Injenus/Inj_Bot_3.0/layout_images/type1.png

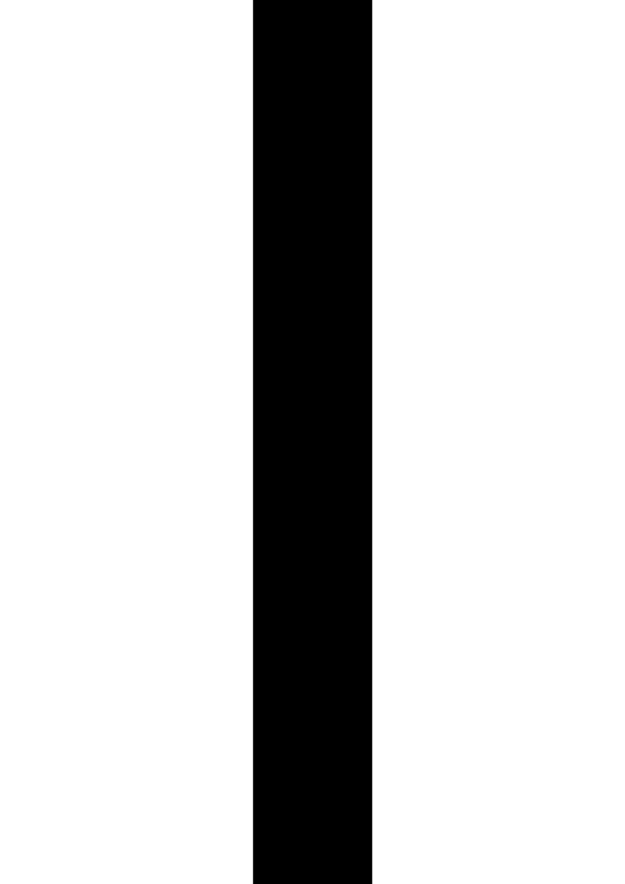
layout_images/type1.png
