Injenus/Inj_Bot_3.0/layout_images/type2.png

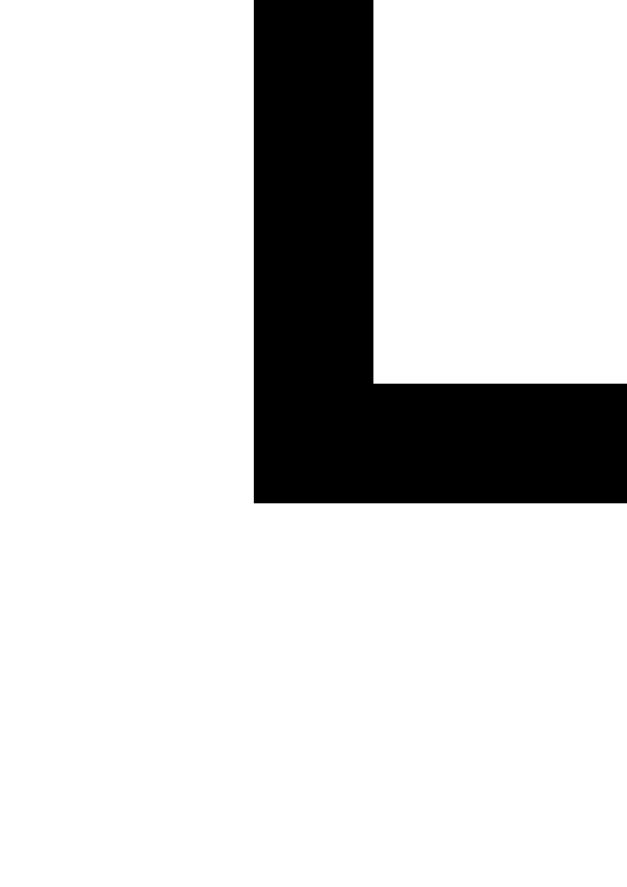
layout_images/type2.png
