Injenus/Inj_Bot_3.0/manipulator_view/workspace_points_1.png

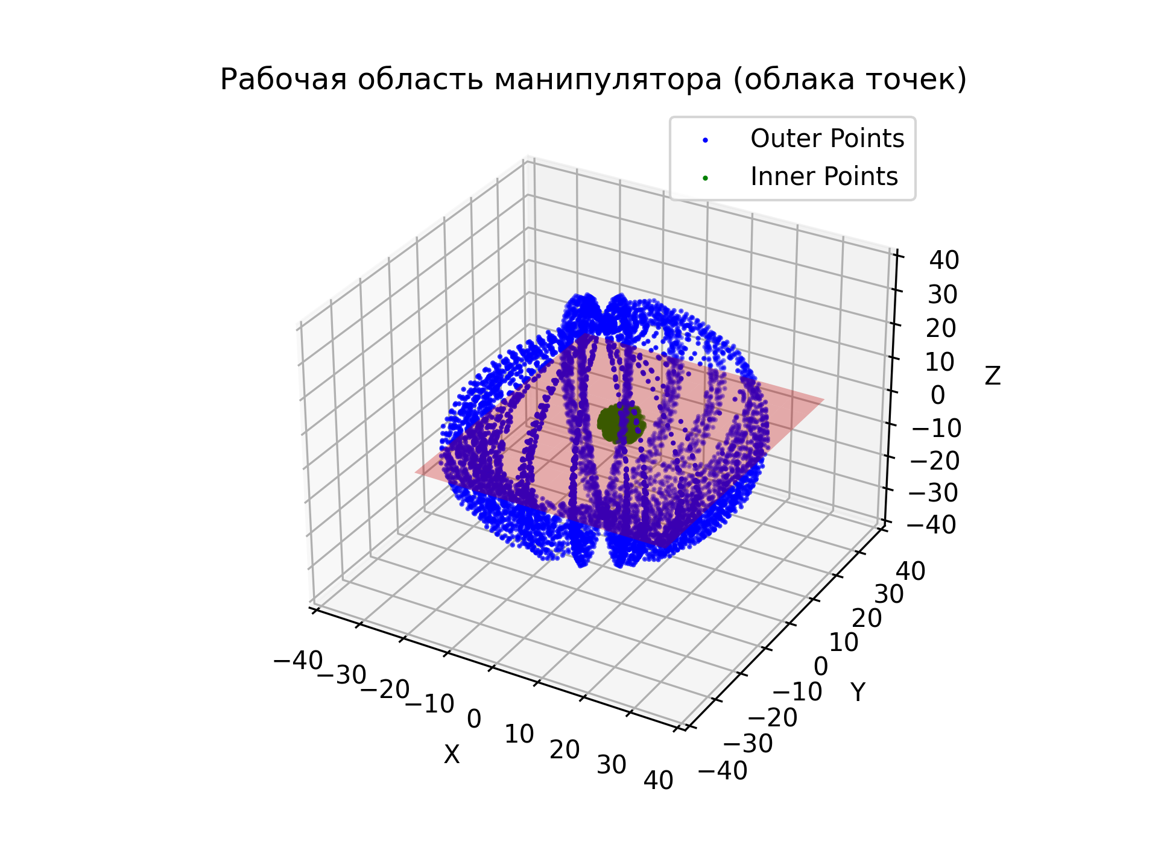
manipulator_view/workspace_points_1.png
