Injenus/Inj_Bot_3.0/manipulator_view/workspace_polygs_1.png

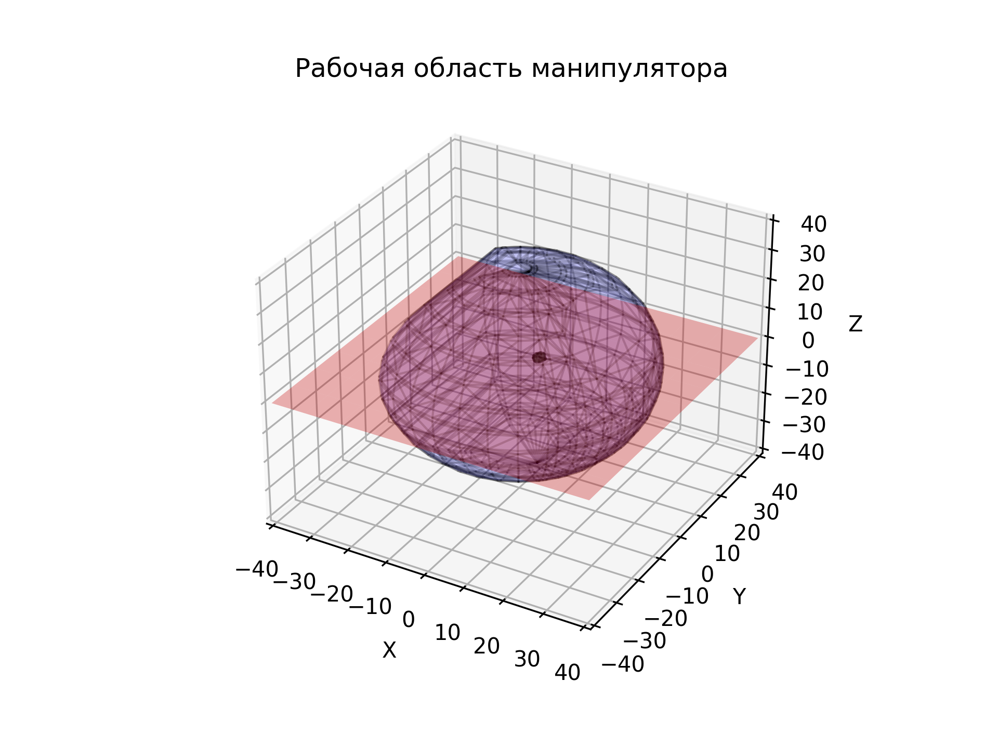
manipulator_view/workspace_polygs_1.png
