Injenus/Inj_Bot_3.0/neural_learn/runs/detect/fruit_detector/confusion_matrix.png

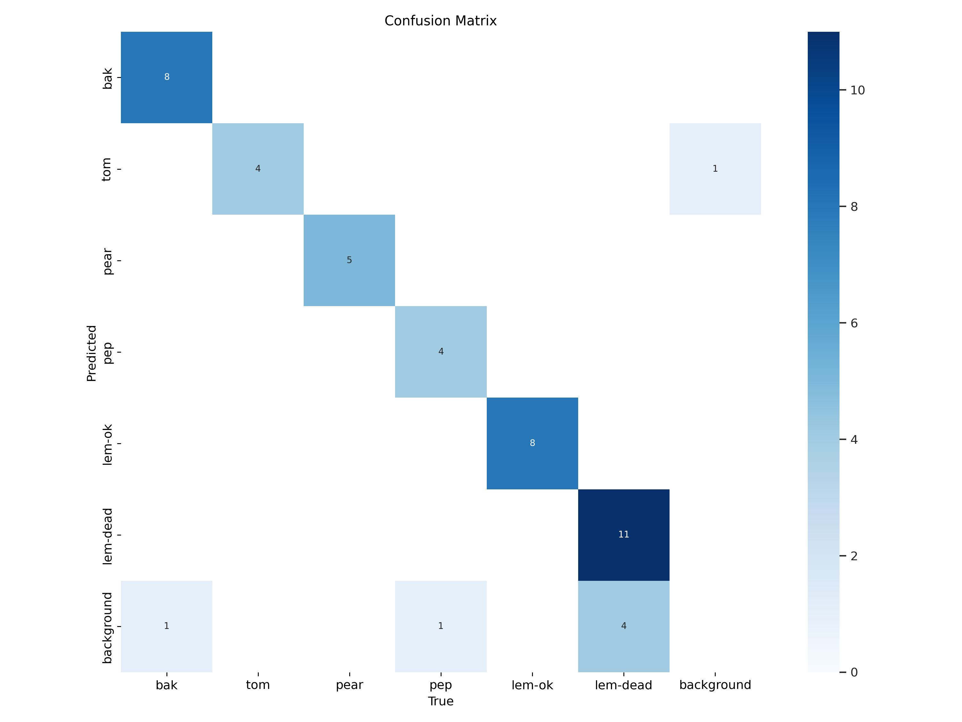
neural_learn/runs/detect/fruit_detector/confusion_matrix.png
