Injenus/Inj_Bot_3.0/neural_learn/runs/detect/fruit_detector/confusion_matrix_normalized.png

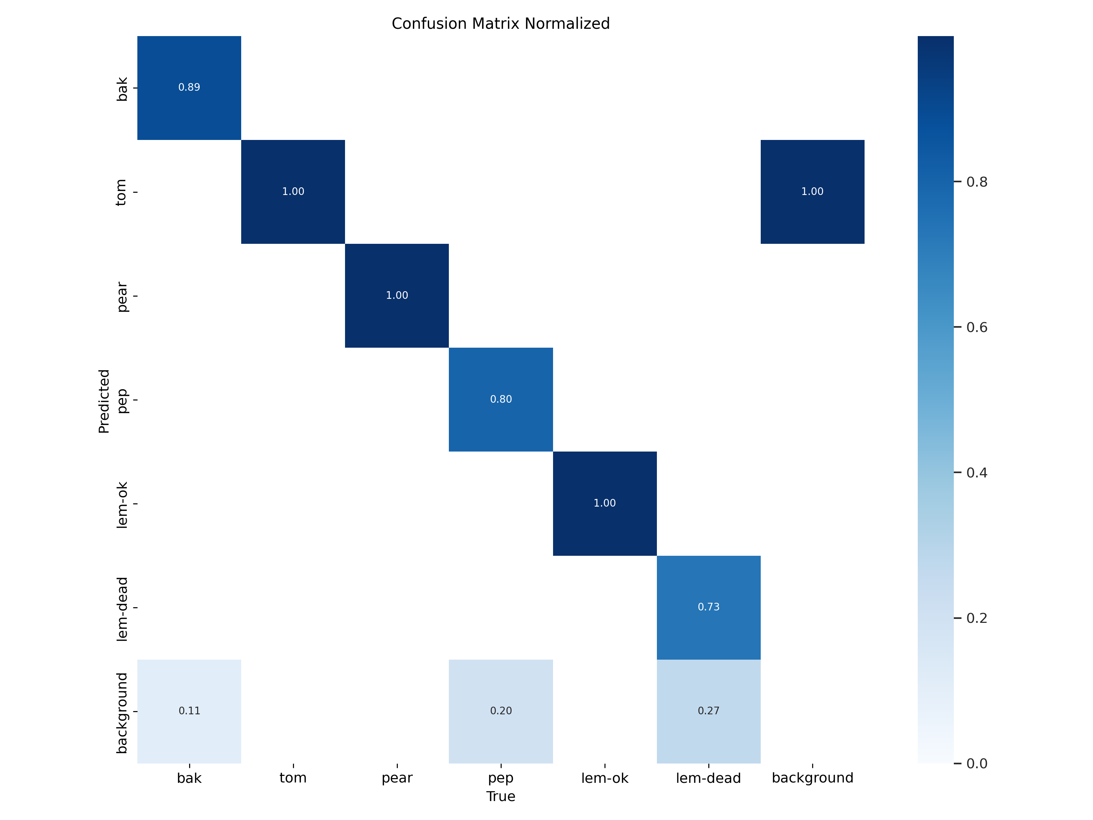
neural_learn/runs/detect/fruit_detector/confusion_matrix_normalized.png
