Injenus/Inj_Bot_3.0/neural_learn/runs/detect/fruit_detector/F1_curve.png

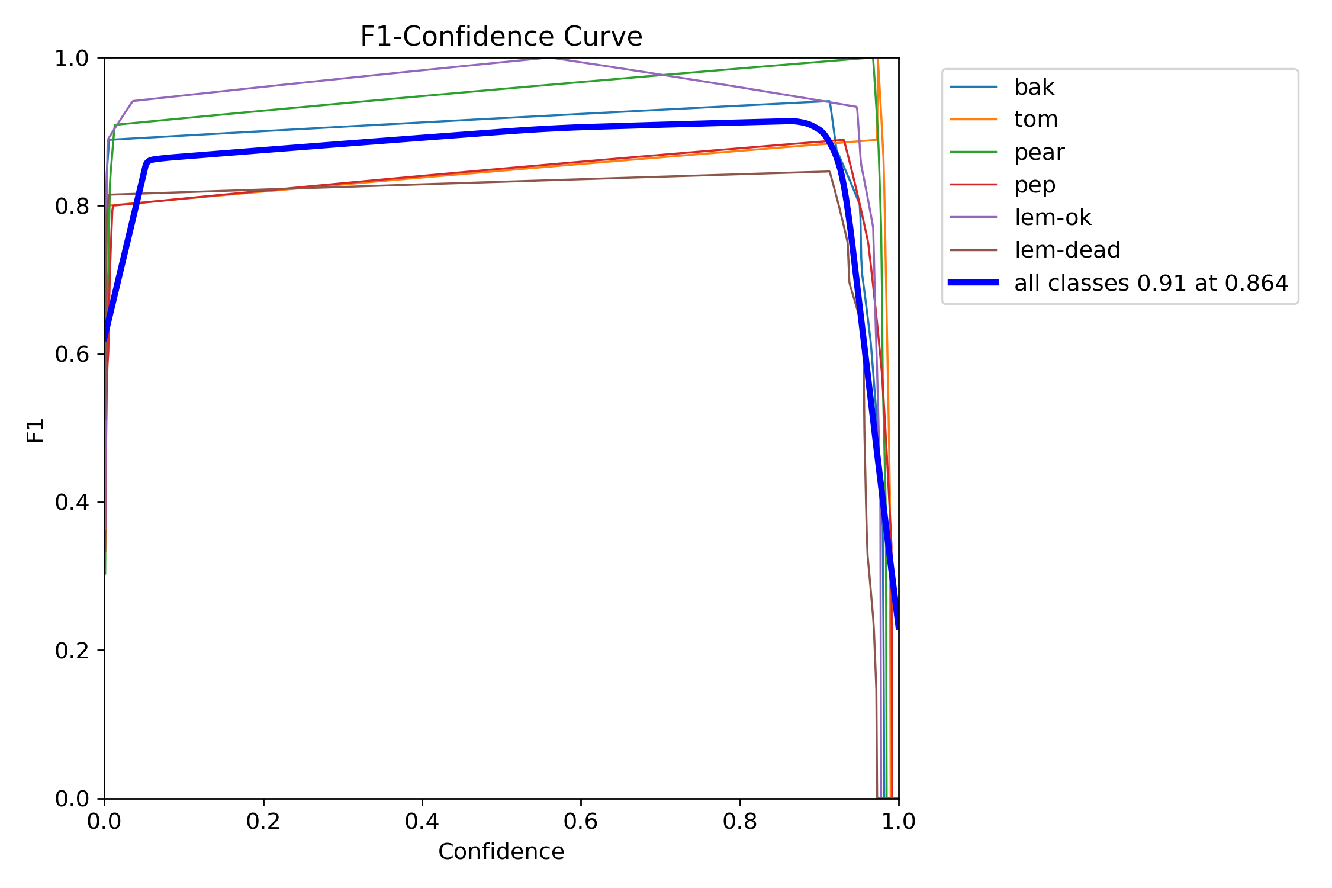
neural_learn/runs/detect/fruit_detector/F1_curve.png
