Injenus/Inj_Bot_3.0/bot_parts/body.stl

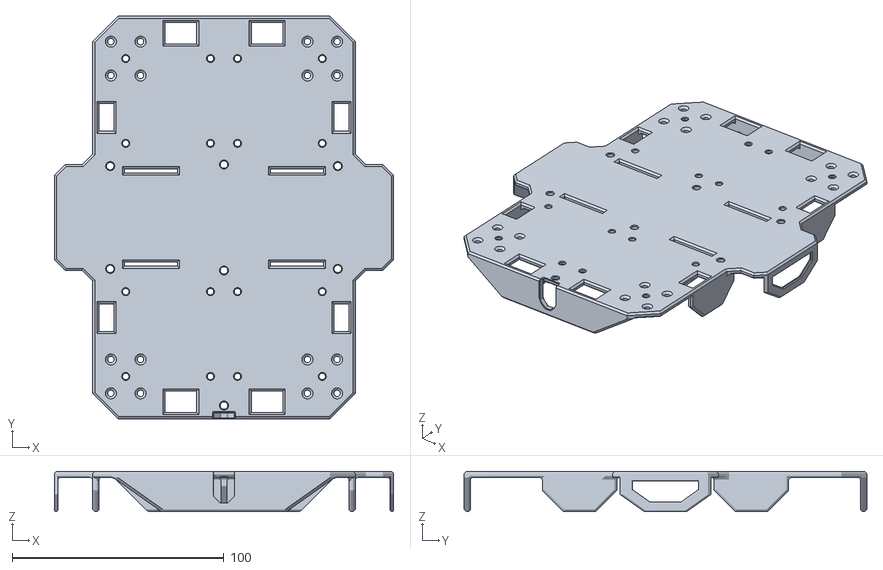
[picture p28: CAD file, 2025-01-23]
bot_parts/body.stl
160.0 x 190.0 x 19.0
