Injenus/Inj_Bot_3.0/bot_parts/stm.stl

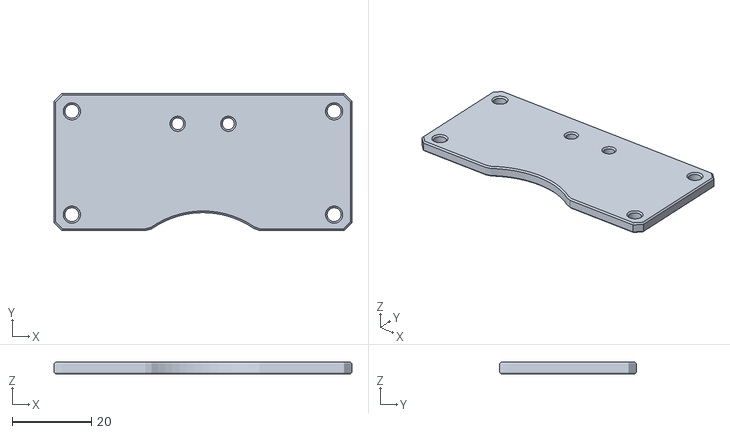
[picture p29: CAD file, 2025-01-23]
bot_parts/stm.stl
75.0 x 34.5 x 3.00
