Injenus/Inj_Bot_3.0/bot_parts/display_test.stl

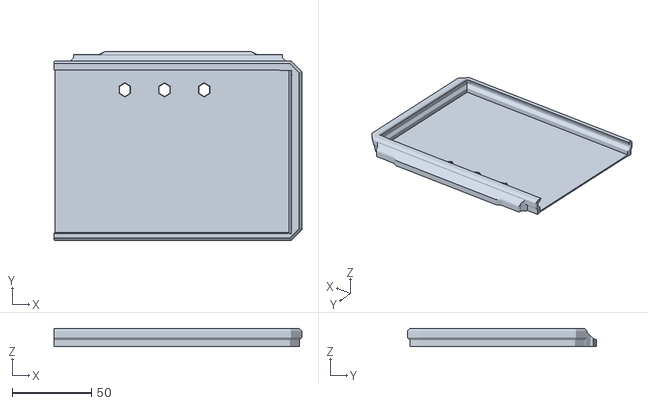
[picture p30: CAD file, 2025-01-23]
bot_parts/display_test.stl
156.5 x 119.4 x 11.6
