Injenus/Inj_Bot_3.0/bot_parts/rpi.stl

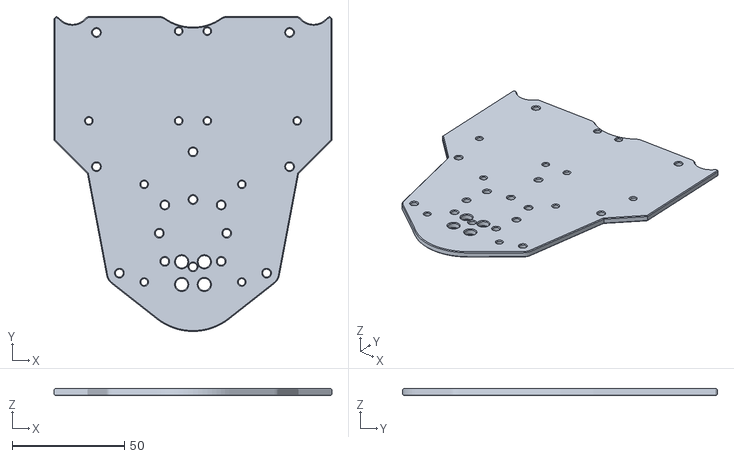
[picture p31: CAD file, 2025-01-23]
bot_parts/rpi.stl
123.7 x 140.3 x 3.00
