Injenus/Inj_Bot_3.0/neural_learn/runs/detect/fruit_detector/results.png

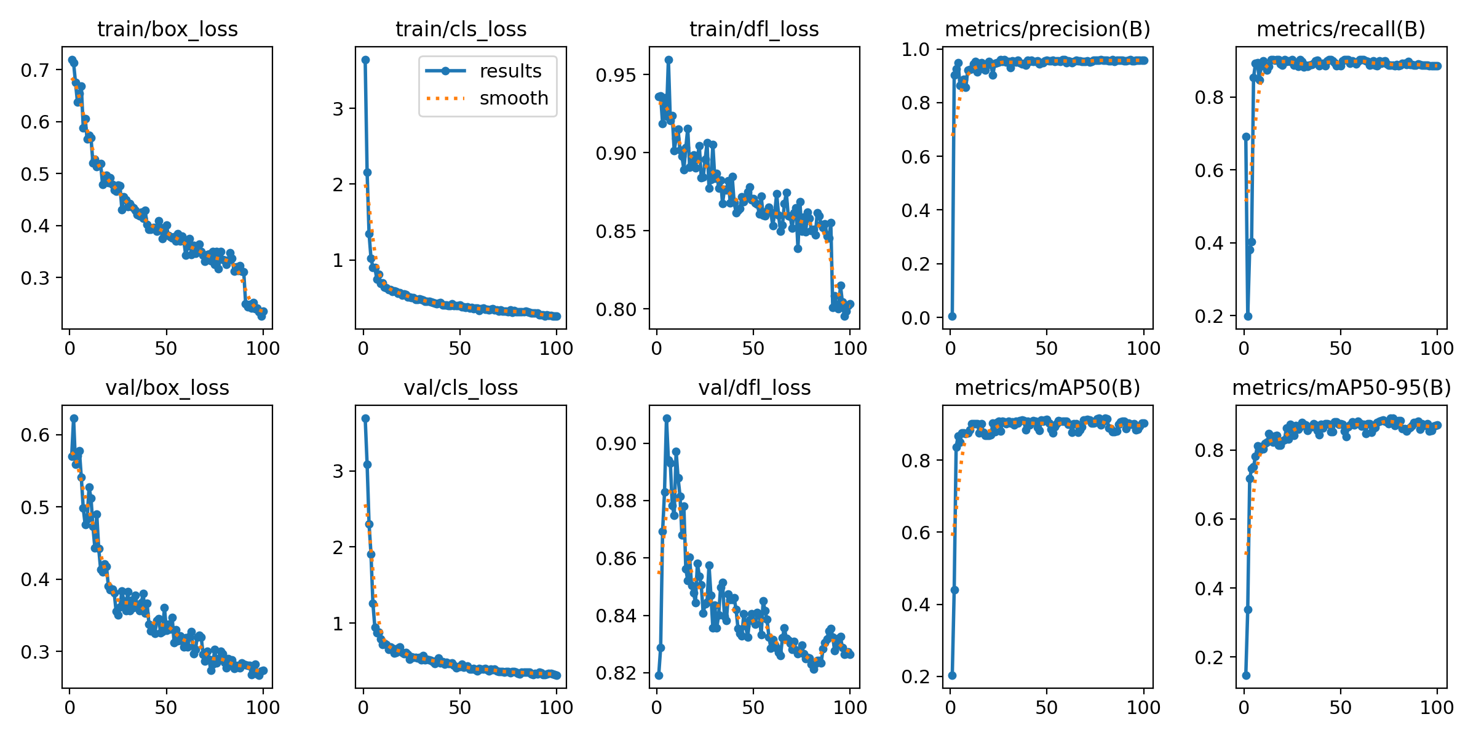
neural_learn/runs/detect/fruit_detector/results.png
