Injenus/Inj_Bot_3.0/ros2_inj_bot_3.0/src/fuck_wheel/fuck_wheel/data_exchange.py

import sys
import os
import rclpy
from rclpy.node import Node
from std_msgs.msg import Int32MultiArray
from std_msgs.msg import String
import serial
import copy
import time

receive_data_path = os.path.join(os.path.expanduser('~'), 'Inj_Bot_3.0', 'wheel_encoder_esp')
if receive_data_path not in sys.path:
    sys.path.append(receive_data_path)

import wheel_modules
############################################
RPM_MULTIPLIER = 8192       ### Убедись, что совпадает с прошивкой!!!
############################################

class WheelSerialReadWrite(Node):
    def __init__(self):
        super().__init__('wheel_read_write')
        self.receive_data_publisher = self.create_publisher(Int32MultiArray,'wheel/current_rpm', 3)
        self.serial_port = None

        self.subscription = self.create_subscription(Int32MultiArray, 'wheel/target_rpm', self.command_callback, 3)
        
        self.last_data = None
        self.send_attempts = 0

        try:
            self.serial_port = serial.Serial(
                port = '/dev/WHEELs',
                baudrate=115200,
                timeout=1
            )
            self.get_logger().info("Serial port opened successfully")
        except serial.SerialException as e:
            self.get_logger().error(f"Failed to open serial port: {e}")

        self.create_timer(0.005, self.main_loop)

        self.ready_pub = self.create_publisher(String, '/nodes_ready', 10)
        msg = String(data = self.get_name())
        self.ready_pub.publish(msg)

    def command_callback(self, msg):
          if self.last_data != msg.data:
              self.last_data = copy.deepcopy(msg.data)
              self.send_attempts = 3


    def main_loop(self):
        while self.send_attempts > 0:
            wheel_modules.send_to_serial(self.serial_port, self.last_data)
            self.send_attempts -= 1

        start_time = time.time()
        max_runtime = 0.025
        intime = True
        rec_buff = bytearray()
        PACKET_LENGTH = 19
        START_BYTE = ord('S')

        parsed = None
        self.serial_port.reset_input_buffer()
        while intime and parsed is None:
            if self.serial_port.in_waiting > 0:
                byte = self.serial_port.read(1)
                rec_buff.append(byte[0])

            # Поиск и обработка полных пакетов
            while True:

                start_pos = -1
                for i in range(len(rec_buff)-1, -1, -1):
                    if rec_buff[i] == START_BYTE:
                        start_pos = i

                # # Поиск стартового байта
                # start_pos = rec_buff.find(START_BYTE.to_bytes(1, 'big'))
                
                if start_pos == -1:
                    # Нет стартового байта - очищаем буфер
                    rec_buff.clear()
                    break
                
                if start_pos > 0:
                    # Удаляем мусор до стартового байта
                    del rec_buff[:start_pos]
                
                if len(rec_buff) < PACKET_LENGTH:
                    # Не хватает данных для полного пакета
                    break
                
                # Извлекаем потенциальный пакет
                packet = rec_buff[:PACKET_LENGTH]
                del rec_buff[:PACKET_LENGTH]
                
                parsed = wheel_modules.parse_packet(packet)
                if parsed is not None:
                    parsed = [round(p/RPM_MULTIPLIER) for p in parsed]
                    #print("Received RPMs:", parsed)
                    break
                else:
                    print("Invalid packet received")

            if time.time() - start_time > max_runtime:
                #print(time.time() - start_time, max_runtime)
                intime = False

        if intime:
            msg = Int32MultiArray()
            msg.data = parsed
            self.receive_data_publisher.publish(msg)
            #self.get_logger().info(f'Publ data: {msg.data}')
        else:
            #self.get_logger().info('Nothing to publ., timeout')
            pass


    def destroy_node(self):
        if self.serial_port and self.serial_port.is_open:
            self.serial_port.close()
        super().destroy_node()


def main(args=None):
    rclpy.init(args=args)
    wheel_data_exchange = WheelSerialReadWrite()
    try:
        rclpy.spin(wheel_data_exchange)
    except:
        wheel_data_exchange.destroy_node()
        rclpy.shutdown()


if __name__ == '__main__':
    main()
