Injenus/Inj_Bot_3.0/lidar_test/pyrplidar_test.py

from pyrplidar import PyRPlidar

lidar = PyRPlidar()
lidar.connect("COM7", baudrate=256000, timeout=3)
# Linux   : "/dev/ttyUSB0"
# MacOS   : "/dev/cu.SLAB_USBtoUART"
# Windows : "COM5"


info = lidar.get_info()
print("info :", info)

health = lidar.get_health()
print("health :", health)

samplerate = lidar.get_samplerate()
print("samplerate :", samplerate)


scan_modes = lidar.get_scan_modes()
print("scan modes :")
for scan_mode in scan_modes:
    print(scan_mode)


lidar.disconnect()
